Dont-Copy-That-Floppy/OpenCellPhone/Images/4.3TFT_TouchDisplay_XY_Values.jpg

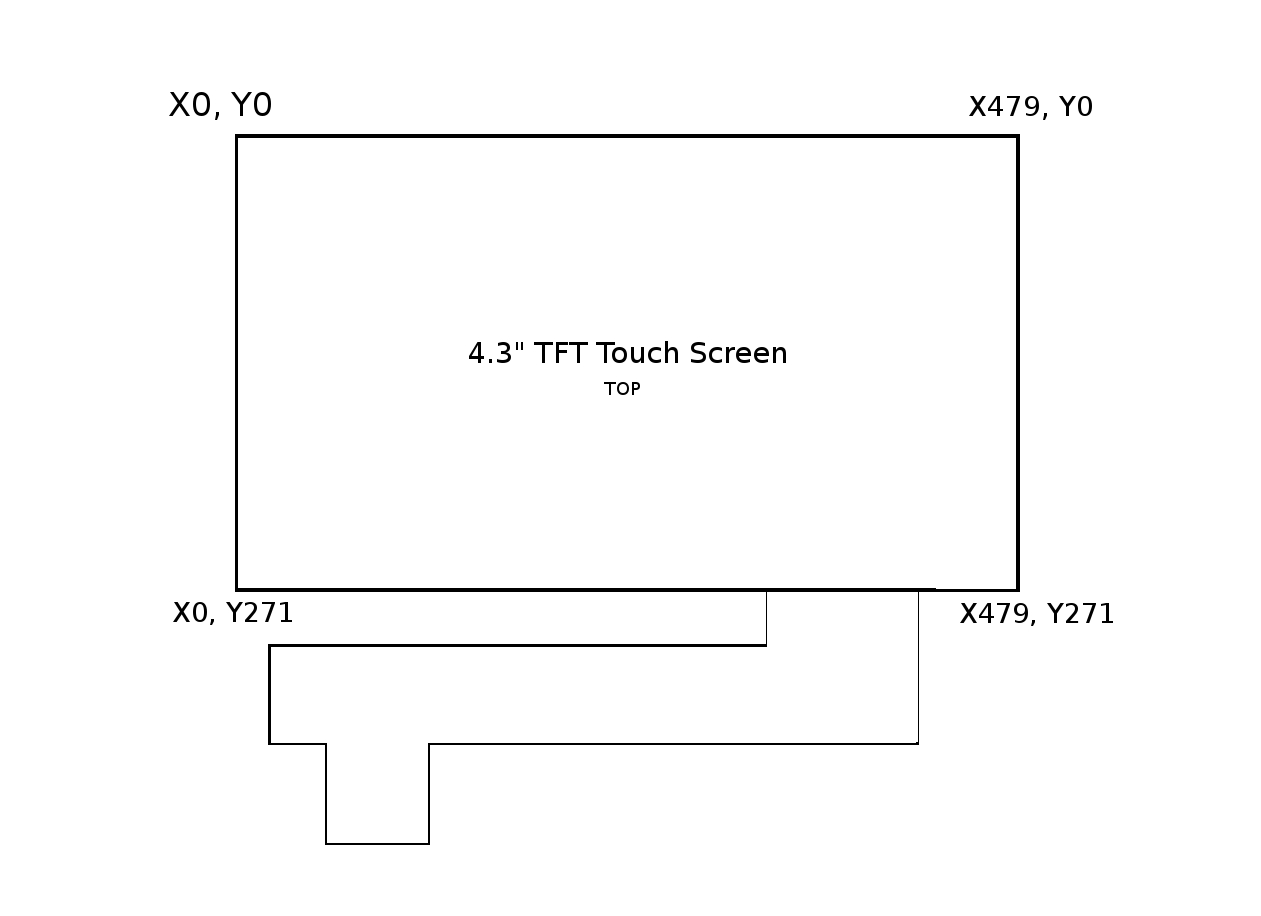
Images/4.3TFT_TouchDisplay_XY_Values.jpg
