Dont-Copy-That-Floppy/OpenCellPhone/Images/Day 1/DSC00150.JPG

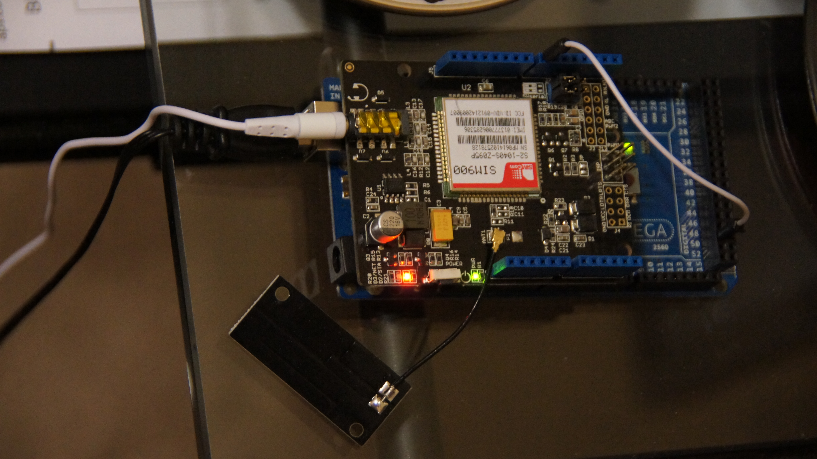
Images/Day 1/DSC00150.JPG
