Dont-Copy-That-Floppy/OpenCellPhone/Images/Day 1/DSC00151.JPG

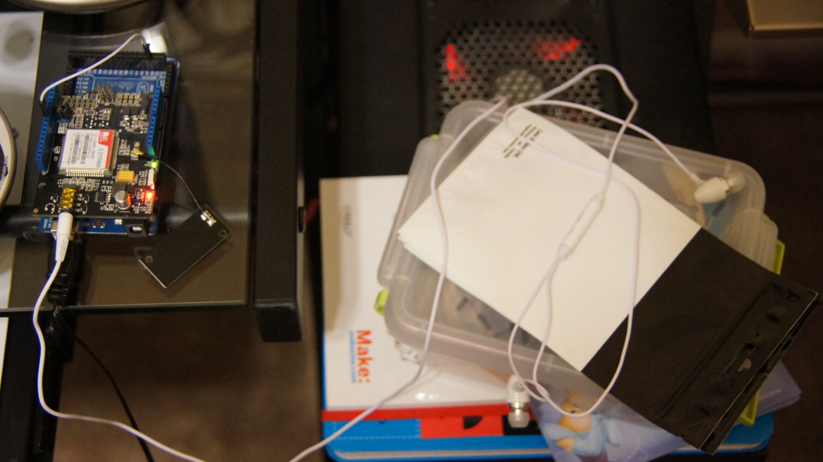
Images/Day 1/DSC00151.JPG
