Dont-Copy-That-Floppy/OpenCellPhone/Images/Day 1/DSC00152.JPG

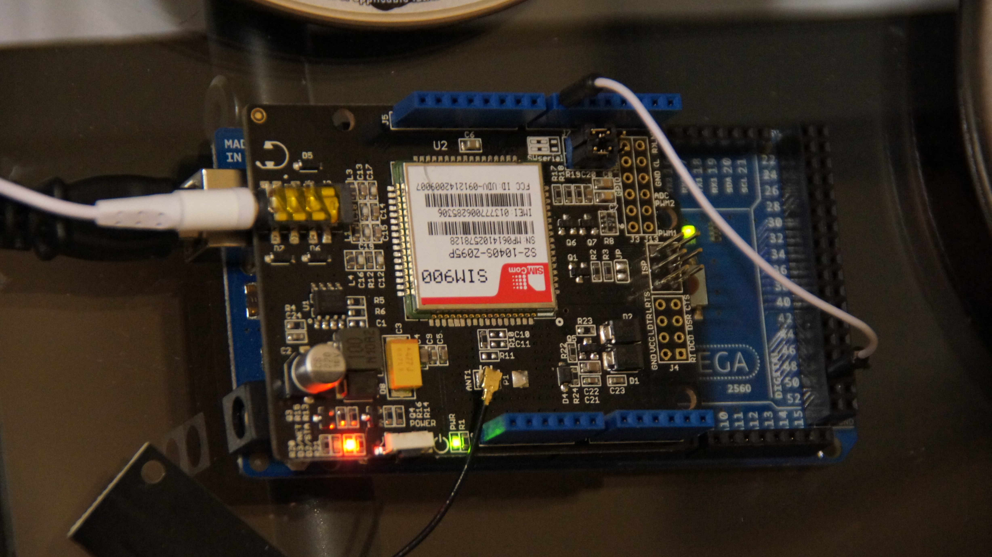
Images/Day 1/DSC00152.JPG
