Dont-Copy-That-Floppy/OpenCellPhone/Images/Day 1/DSC00153.JPG

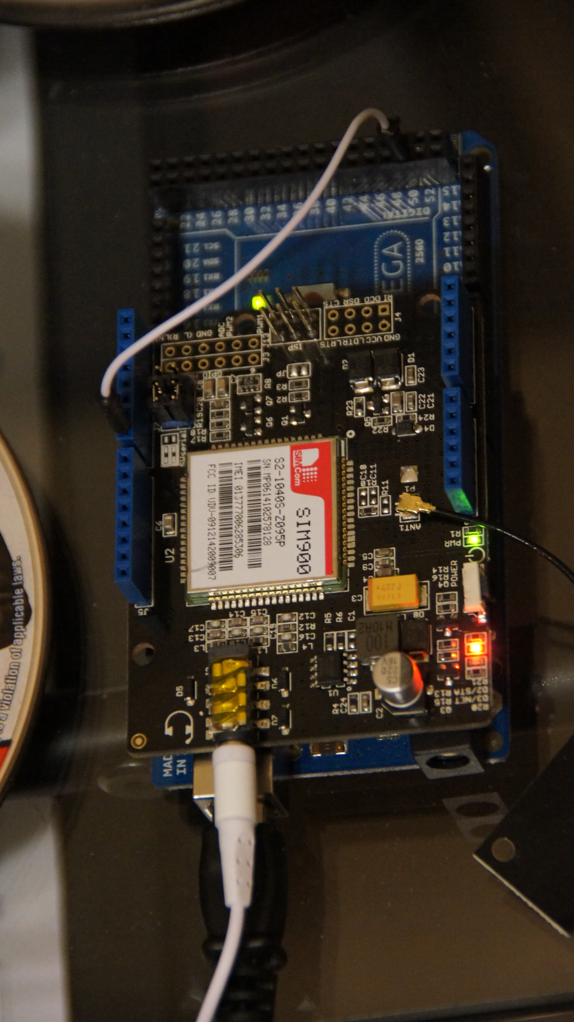
Images/Day 1/DSC00153.JPG
