Dont-Copy-That-Floppy/OpenCellPhone/Images/DSC04776.JPG

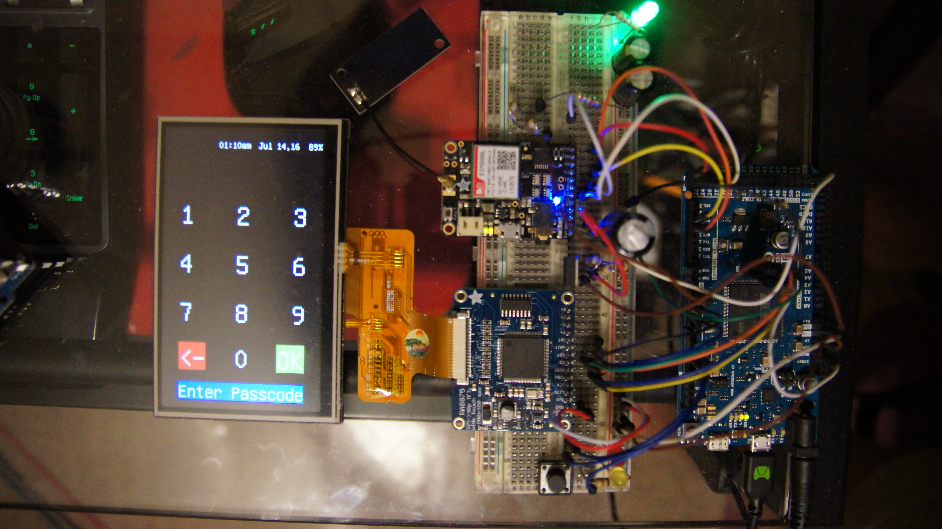
Images/DSC04776.JPG
