Dont-Copy-That-Floppy/OpenCellPhone/Images/DSC04777.JPG

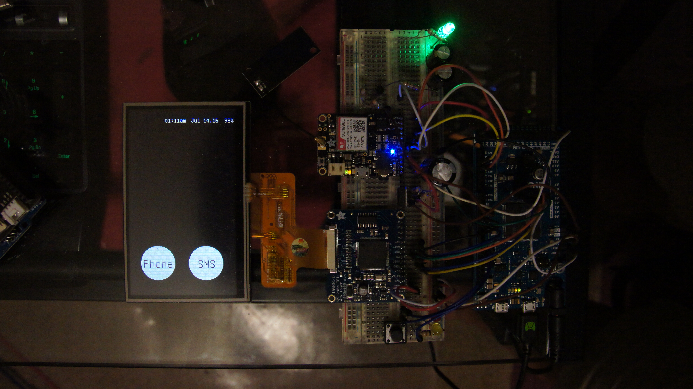
Images/DSC04777.JPG
