Dont-Copy-That-Floppy/OpenCellPhone/Images/Pre-Protoype.JPG

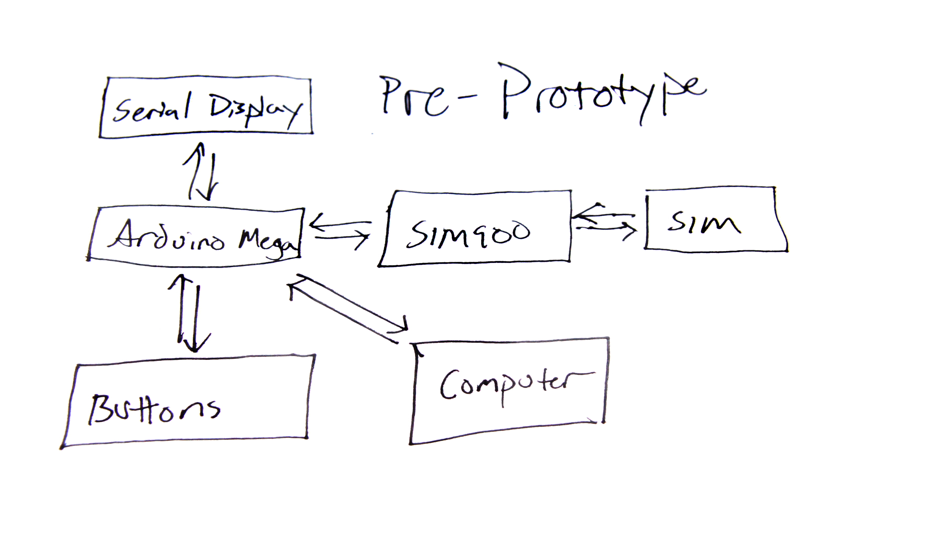
Images/Pre-Protoype.JPG
