Dont-Copy-That-Floppy/OpenCellPhone/Images/Prototype.JPG

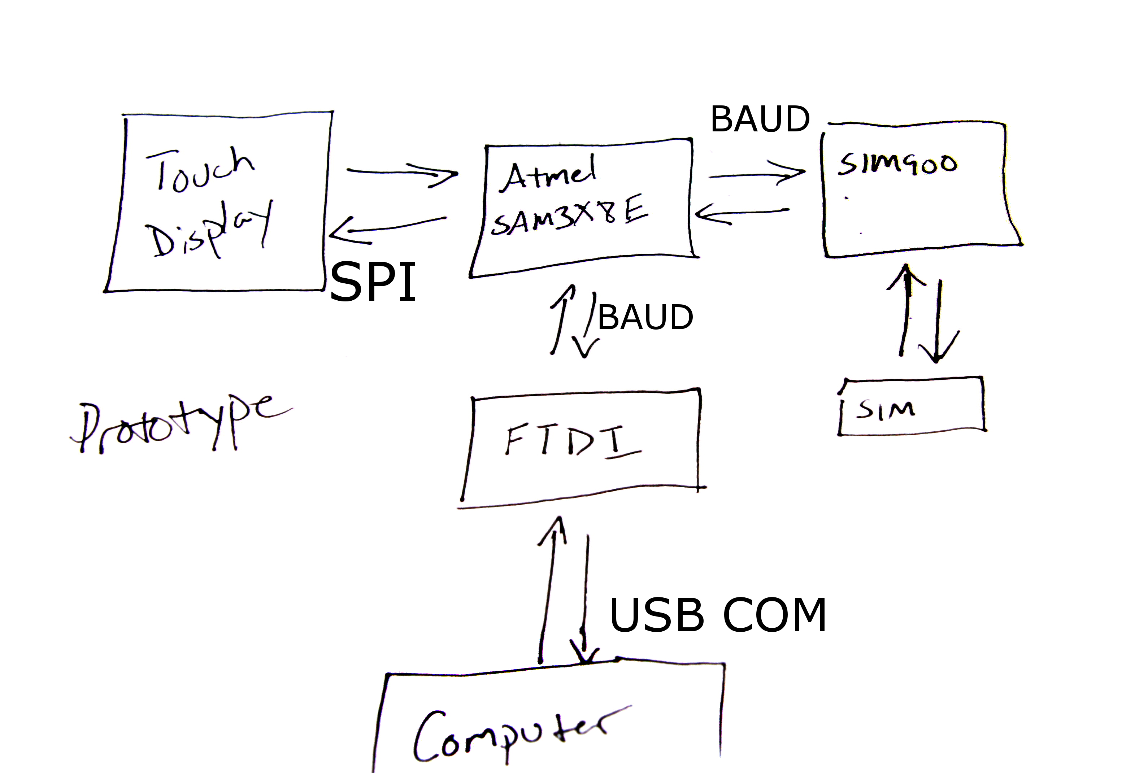
Images/Prototype.JPG
