Dont-Copy-That-Floppy/OpenCellPhone/Images/Prototype_8-19-2014.JPG

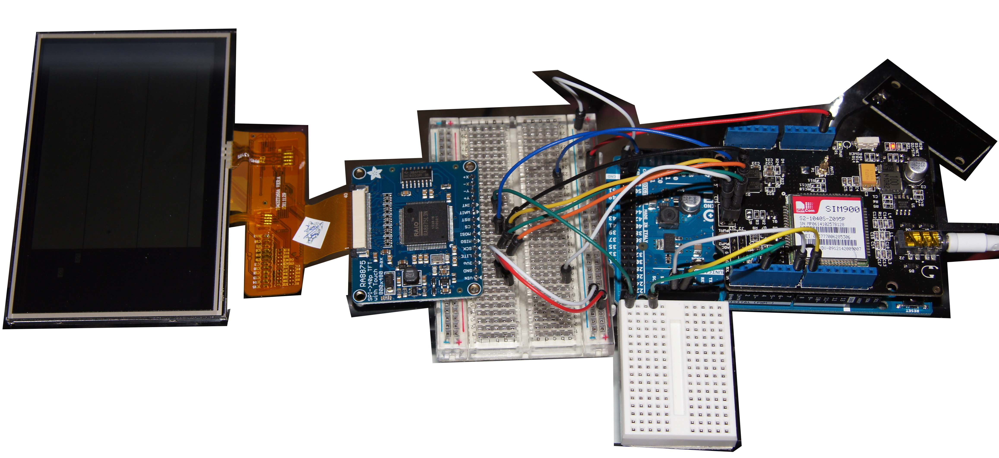
Images/Prototype_8-19-2014.JPG
