Dont-Copy-That-Floppy/OpenCellPhone/Images/Screen Pictures/Answer_Screen.JPG

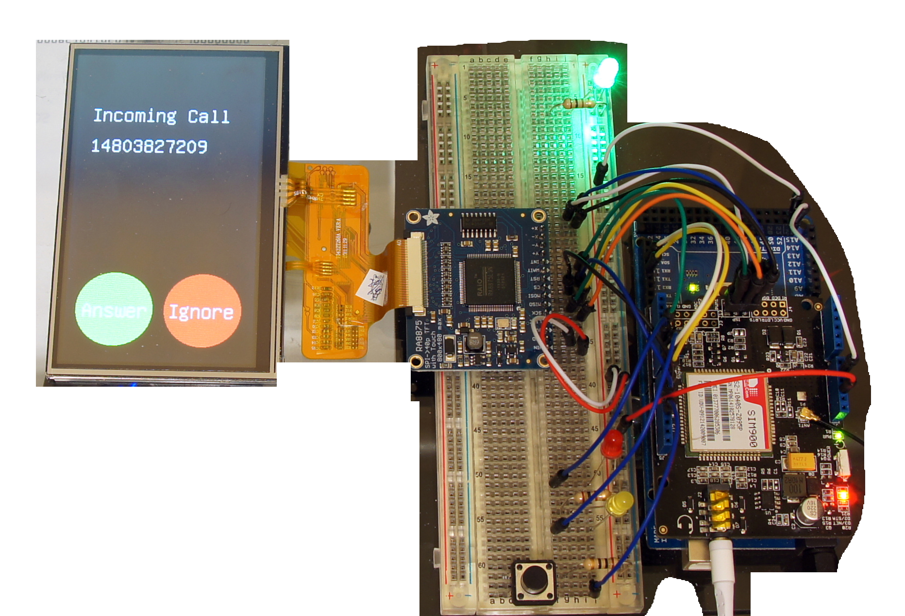
Images/Screen Pictures/Answer_Screen.JPG
