Dont-Copy-That-Floppy/OpenCellPhone/Images/Screen Pictures/Boot_Screen.JPG

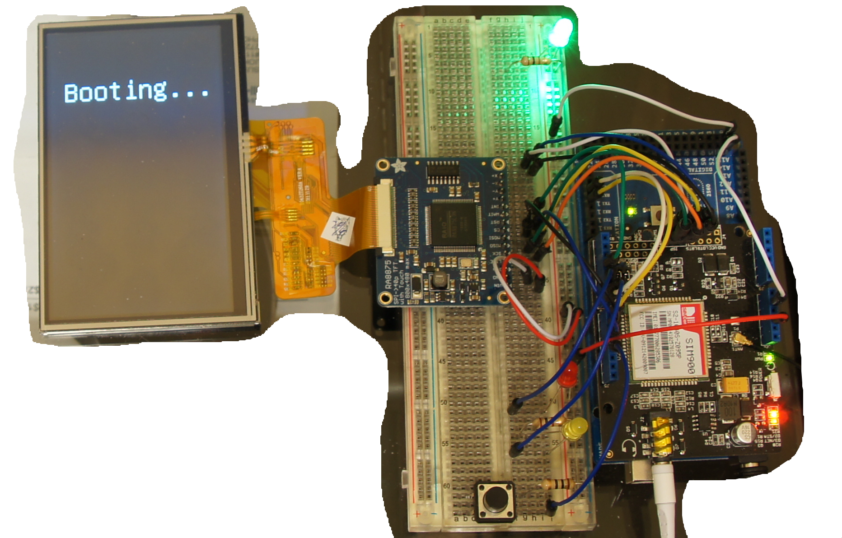
Images/Screen Pictures/Boot_Screen.JPG
