Dont-Copy-That-Floppy/OpenCellPhone/Images/Screen Pictures/Boot_Screen_PowerDown.JPG

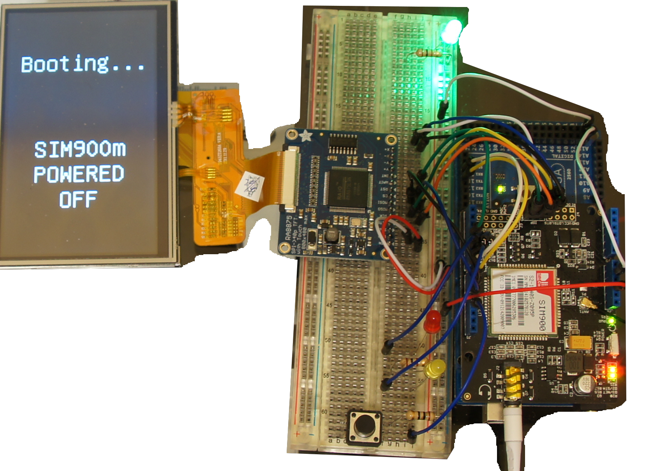
Images/Screen Pictures/Boot_Screen_PowerDown.JPG
