Dont-Copy-That-Floppy/OpenCellPhone/Images/Screen Pictures/Home_Screen.JPG

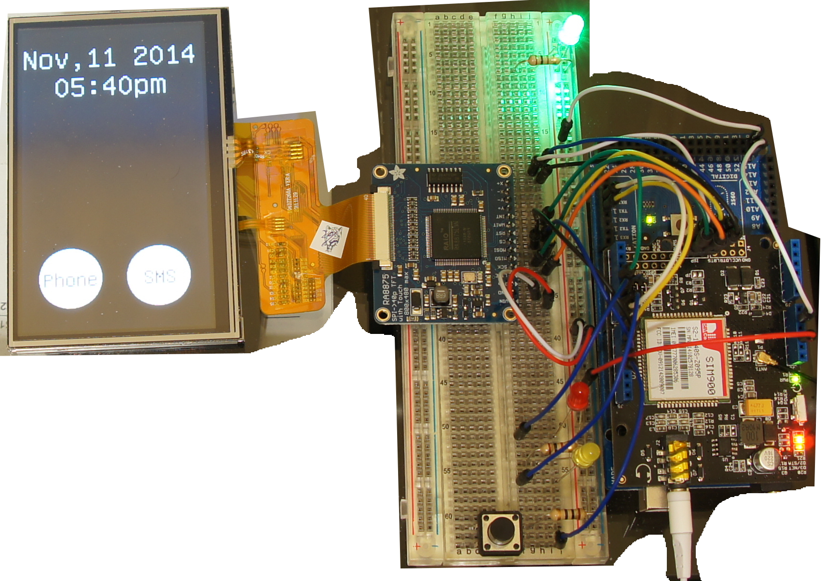
Images/Screen Pictures/Home_Screen.JPG
