Dont-Copy-That-Floppy/OpenCellPhone/Images/Screen Pictures/Passcode_Entered.JPG

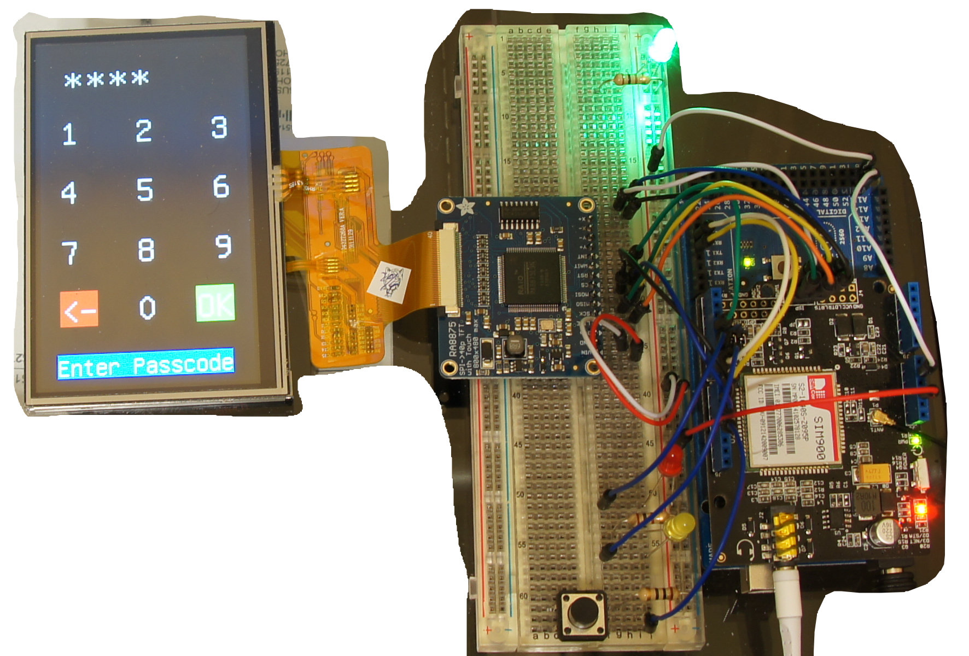
Images/Screen Pictures/Passcode_Entered.JPG
