Dont-Copy-That-Floppy/OpenCellPhone/Images/Screen Pictures/Ready_Screen.JPG

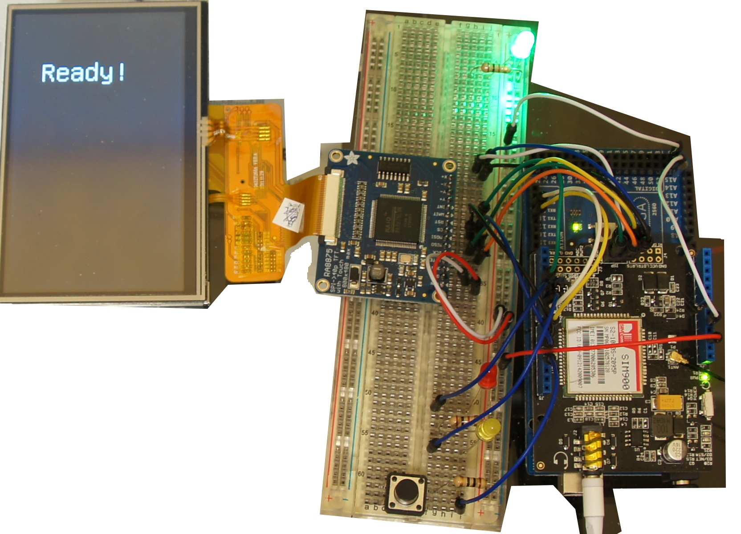
Images/Screen Pictures/Ready_Screen.JPG
