Dont-Copy-That-Floppy/OpenCellPhone/Images/ThePhone08162014.JPG

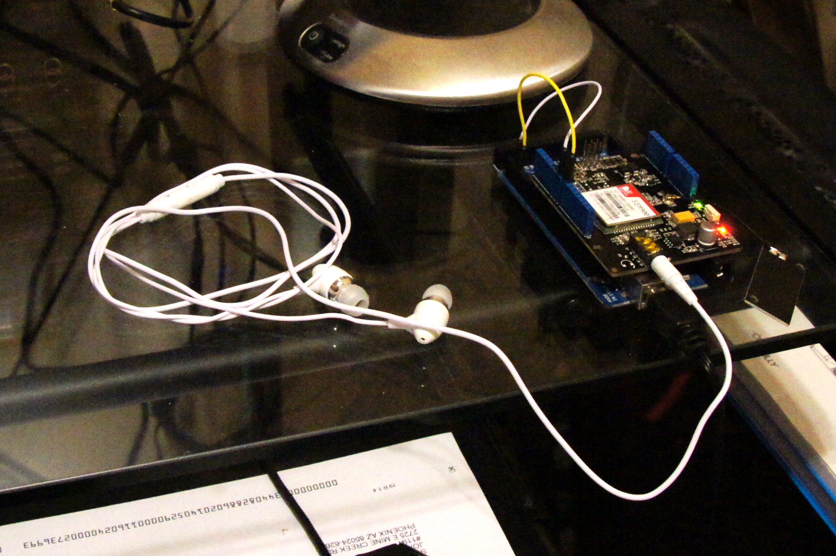
Images/ThePhone08162014.JPG
